emeb/RP2040_Audio/Firmware/dblfilter.h

/* Included by my_resample.c */
#define MY_FILTER_NMULT ((short)26)
#define MY_FILTER_SCALE 13128 /* Unity-gain scale factor */
#define MY_FILTER_NWING 3072 /* Filter table length */
static short MY_FILTER_IMP[] /* Impulse response */ = {
-1,
-1,
-1,
-1,
-1,
-1,
-1,
-1,
-1,
-1,
-1,
-1,
-1,
-1,
-1,
-1,
-1,
-1,
-1,
-1,
-1,
-1,
-2,
-2,
-2,
-2,
-2,
-2,
-2,
-2,
-2,
-2,
-2,
-2,
-2,
-2,
-2,
-2,
-2,
-2,
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
};
