emeb/RP2040_Audio/Firmware/splash.h

unsigned char splash_png_565[] = {
  0x9d, 0xdd, 0x8d, 0x7c, 0x95, 0xbd, 0x95, 0xbe, 0x95, 0xbd, 0x95, 0xbe,
  0x95, 0xdd, 0x95, 0xbe, 0x95, 0xbe, 0x85, 0x7d, 0x85, 0x7d, 0x85, 0x7e,
  0x95, 0xde, 0x95, 0xff, 0xa5, 0xfe, 0x9d, 0xdf, 0xa6, 0x1f, 0x9d, 0xff,
  0xa6, 0x1f, 0xa6, 0x1f, 0xa6, 0x3f, 0xa6, 0x1f, 0xa6, 0x3f, 0x9e, 0x1f,
  0x96, 0x1f, 0x8d, 0xff, 0xa6, 0x1e, 0xa6, 0x3f, 0xae, 0x7e, 0xae, 0x5f,
  0xae, 0x7e, 0xae, 0x5f, 0xae, 0x7e, 0xae, 0x7f, 0xb6, 0x9f, 0xb6, 0x9f,
  0xb6, 0x9f, 0xb6, 0x9f, 0xb6, 0x9f, 0xae, 0x5f, 0xa6, 0x5e, 0xa6, 0x7f,
  0xbe, 0xbe, 0xbe, 0xbf, 0xbe, 0xbe, 0xbe, 0xbf, 0xbe, 0xde, 0xbe, 0xbf,
  0xbe, 0xbe, 0xbe, 0xbf, 0xc6, 0xde, 0xbe, 0xdf, 0xc6, 0xde, 0xc6, 0xdf,
  0xbe, 0xff, 0xae, 0x7e, 0xa6, 0x5e, 0xae, 0x9f, 0xc6, 0xdf, 0xc6, 0xbf,
  0xc6, 0xff, 0xc6, 0xff, 0xc6, 0xff, 0xbe, 0xdf, 0xc6, 0xfe, 0xc6, 0xff,
  0xc6, 0xfe, 0xc6, 0xff, 0xc6, 0xfe, 0xc6, 0xff, 0xc6, 0xff, 0xbe, 0x9f,
  0xa6, 0x9e, 0xa6, 0x9f, 0xbe, 0xbf, 0xc6, 0xdf, 0xc6, 0xff, 0xc6, 0xdf,
  0xc6, 0xff, 0xc6, 0xdf, 0xc6, 0xff, 0xc6, 0xdf, 0xc6, 0xff, 0xc6, 0xdf,
  0xc6, 0xff, 0xc6, 0xdf, 0xc6, 0xff, 0xc6, 0xdf, 0xc6, 0xff, 0xc6, 0xdf,
  0xc6, 0xff, 0xc6, 0xdf, 0xc6, 0xff, 0xc6, 0xdf, 0xc6, 0xff, 0xc6, 0xdf,
  0xc6, 0xff, 0xc6, 0xdf, 0xc6, 0xff, 0xc6, 0xdf, 0xc6, 0xff, 0xc6, 0xdf,
  0xc6, 0xff, 0xc6, 0xdf, 0xc6, 0xff, 0xc6, 0xdf, 0xc6, 0xff, 0xc6, 0xdf,
  0xc6, 0xff, 0xc6, 0xdf, 0xc6, 0xff, 0xc6, 0xdf, 0xc6, 0xff, 0xc6, 0xdf,
  0xc6, 0xff, 0xc6, 0xdf, 0xc6, 0xff, 0xc6, 0xdf, 0xc6, 0xff, 0xc6, 0xdf,
  0xc6, 0xff, 0xc6, 0xdf, 0xc6, 0xff, 0xc6, 0xdf, 0xc6, 0xff, 0xc6, 0xdf,
  0xc6, 0xff, 0xc6, 0xdf, 0xc6, 0xff, 0xc6, 0xdf, 0xc6, 0xff, 0xc6, 0xdf,
  0xc6, 0xff, 0xc6, 0xdf, 0xc6, 0xff, 0xc6, 0xdf, 0xc6, 0xff, 0xc6, 0xdf,
  0xc6, 0xff, 0xc6, 0xdf, 0xc6, 0xff, 0xc6, 0xdf, 0xc6, 0xff, 0xc6, 0xdf,
  0xc6, 0xff, 0xc6, 0xdf, 0xc6, 0xff, 0xc6, 0xdf, 0xc6, 0xff, 0xc6, 0xdf,
  0xc6, 0xff, 0xc6, 0xdf, 0xc6, 0xff, 0xc6, 0xdf, 0xc6, 0xff, 0xc6, 0xdf,
  0xc6, 0xff, 0xc6, 0xdf, 0xc6, 0xff, 0xc6, 0xdf, 0x95, 0x7c, 0x95, 0x9c,
  0x95, 0x7d, 0x9d, 0x9d, 0x95, 0x9d, 0x9d, 0xbd, 0x9d, 0xbe, 0x9d, 0xbd,
  0x95, 0xbe, 0x8d, 0x7d, 0x85, 0x5d, 0x8d, 0x7d, 0x95, 0xbe, 0x9d, 0xfe,
  0x9d, 0xfe, 0xa5, 0xfe, 0x9d, 0xfe, 0xa5, 0xfe, 0xa6, 0x1f, 0xa6, 0x1e,
  0xa6, 0x1f, 0xa6, 0x3e, 0xa6, 0x3f, 0xa6, 0x1e, 0x95, 0xff, 0x95, 0xfe,
  0x9e, 0x1e, 0xa6, 0x5f, 0xae, 0x5f, 0xae, 0x7e, 0xae, 0x5f, 0xb6, 0x5e,
  0xae, 0x5f, 0xb6, 0x7e, 0xae, 0x7f, 0xb6, 0x9f, 0xb6, 0x9f, 0xbe, 0x9e,
  0xb6, 0x7f, 0xae, 0x5e, 0xa6, 0x1e, 0xa6, 0x3d, 0xad, 0xdc, 0x9d, 0x59,
  0x8d, 0x18, 0x8c, 0xf7, 0x84, 0xd7, 0x8d, 0x17, 0x95, 0x38, 0x95, 0x37,
  0xa5, 0x9a, 0x9d, 0x59, 0x9d, 0x59, 0xa5, 0xba, 0x9d, 0xba, 0xad, 0xfb,
  0xa6, 0x1d, 0xb6, 0x9e, 0xc6, 0xbf, 0xc6, 0xde, 0xc6, 0xdf, 0xce, 0xfe,
  0xc6, 0xdf, 0xc6, 0xde, 0xc6, 0xdf, 0xce, 0xfe, 0xc6, 0xff, 0xce, 0xfe,
  0xc6, 0xdf, 0xce, 0xfe, 0xc6, 0xdf, 0xc6, 0xbe, 0xae, 0x5e, 0xb6, 0x9e,
  0xbe, 0xbf, 0xc6, 0xdf, 0xc6, 0xdf, 0xce, 0xde, 0xc6, 0xdf, 0xce, 0xde,
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
};
unsigned int splash_png_565_len = 25600;
