emeb/RP2040_Audio/Firmware/debounce.h

/*
 * debounce.h - simple button debouncer
 * E. Brombaugh 07-07-2019
 */

#ifndef __debounce__
#define __debounce__

#include <stdint.h>

typedef struct
{
	uint16_t pipe;
	uint8_t state;
	uint8_t prev_state;
	uint8_t re;
	uint8_t fe;
	uint16_t mask;
} debounce_state;

void init_debounce(debounce_state *dbs, uint8_t len);
void debounce(debounce_state *dbs, uint32_t in);

#endif
